suppersimon-py/Squirrel-Net/firmware/meshtastic/src/configuration.h

#pragma once
#include <Arduino.h>
#ifdef RV3028_RTC
#include "Melopero_RV3028.h"
#endif
#ifdef PCF8563_RTC
#include "pcf8563.h"
#endif
#ifndef APP_VERSION
#error APP_VERSION must be set by the build environment
#endif
#define HW_VERSION "1.0"
#define xstr(s) ystr(s)
#define ystr(s) #s
#define optstr(s) (xstr(s)[0] ? xstr(s) : "unset")
#define EXT_RAM_ATTR
#define IRAM_ATTR
#define RTC_DATA_ATTR
#define EXT_RAM_BSS_ATTR EXT_RAM_ATTR
#define TX_GAIN_LORA 0
#if defined(SEEED_WIO_TRACKER_L1)
#define SSD1306_ADDRESS 0x3D
#define USE_SH1106
#else
#define SSD1306_ADDRESS 0x3C
#endif
#define ST7567_ADDRESS 0x3F
#define CARDKB_ADDR 0x5F
#define TDECK_KB_ADDR 0x55
#define BBQ10_KB_ADDR 0x1F
#define MPR121_KB_ADDR 0x5A
#define BME_ADDR 0x76
#define BME_ADDR_ALTERNATE 0x77
#define MCP9808_ADDR 0x18
#define INA_ADDR 0x40
#define INA_ADDR_ALTERNATE 0x41
#define INA_ADDR_WAVESHARE_UPS 0x43
#define INA3221_ADDR 0x42
#define MAX1704X_ADDR 0x36
#define QMC6310_ADDR 0x1C
#define QMI8658_ADDR 0x6B
#define QMC5883L_ADDR 0x0D
#define HMC5883L_ADDR 0x1E
#define SHTC3_ADDR 0x70
#define LPS22HB_ADDR 0x5C
#define LPS22HB_ADDR_ALT 0x5D
#define SHT31_4x_ADDR 0x44
#define SHT31_4x_ADDR_ALT 0x45
#define PMSA0031_ADDR 0x12
#define QMA6100P_ADDR 0x12
#define AHT10_ADDR 0x38
#define RCWL9620_ADDR 0x57
#define VEML7700_ADDR 0x10
#define TSL25911_ADDR 0x29
#define OPT3001_ADDR 0x45
#define OPT3001_ADDR_ALT 0x44
#define MLX90632_ADDR 0x3A
#define DFROBOT_LARK_ADDR 0x42
#define DFROBOT_RAIN_ADDR 0x1d
#define NAU7802_ADDR 0x2A
#define MAX30102_ADDR 0x57
#define MLX90614_ADDR_DEF 0x5A
#define CGRADSENS_ADDR 0x66
#define LTR390UV_ADDR 0x53
#define XPOWERS_AXP192_AXP2101_ADDRESS 0x34 // same adress as TCA8418
#define PCT2075_ADDR 0x37
#define MPU6050_ADDR 0x68
#define STK8BXX_ADDR 0x18
#define LIS3DH_ADDR 0x18
#define LIS3DH_ADDR_ALT 0x19
#define BMA423_ADDR 0x19
#define LSM6DS3_ADDR 0x6A
#define BMX160_ADDR 0x69
#define ICM20948_ADDR 0x69
#define ICM20948_ADDR_ALT 0x68
#define NCP5623_ADDR 0x38
#define LP5562_ADDR 0x30
#define TCA9535_ADDR 0x20
#define TCA9555_ADDR 0x26
#define FT6336U_ADDR 0x48
#define TPS65233_ADDR 0x60
#define COLOR565(r, g, b) (((r & 0xF8) << 8) | ((g & 0xFC) << 3) | ((b & 0xF8) >> 3))
#include "variant.h"
#if defined(VEXT_ENABLE) && !defined(VEXT_ON_VALUE)
#define VEXT_ON_VALUE LOW
#endif
#define GPS_BAUDRATE 9600
#define GPS_BAUDRATE_FIXED 0
#define GPS_THREAD_INTERVAL 200
#include "architecture.h"
#define DEFAULT_REBOOT_SECONDS 7
#define DEFAULT_SHUTDOWN_SECONDS 2
#define MINIMUM_SAFE_FREE_HEAP 1500
#if defined(I2C_SDA1) || defined(PIN_WIRE1_SDA)
#define WIRE_INTERFACES_COUNT 2
#elif HAS_WIRE
#define WIRE_INTERFACES_COUNT 1
#endif
#define HAS_WIFI 0
#define HAS_ETHERNET 0
#define HAS_SCREEN 0
#define HAS_TFT 0
#define HAS_WIRE 0
#define HAS_GPS 0
#define HAS_BUTTON 0
#define HAS_TRACKBALL 0
#define HAS_TOUCHSCREEN 0
#define HAS_TELEMETRY 0
#define HAS_SENSOR 0
#define HAS_RADIO 0
#define HAS_RTC 0
#define HAS_CPU_SHUTDOWN 0
#define HAS_BLUETOOTH 0
#ifndef HW_VENDOR
#error HW_VENDOR must be defined
#endif
#if defined(HAS_NCP5623) || defined(HAS_LP5562) || defined(RGBLED_RED) || defined(HAS_NEOPIXEL) || defined(UNPHONE)
#define HAS_RGB_LED
#endif
#define HAS_NETWORKING (HAS_WIFI || HAS_ETHERNET)
#include "DebugConfiguration.h"
#include "RF95Configuration.h"
